EPICmynamesBG/WiFi-USB/firmware/data/power_button_gray_512.png

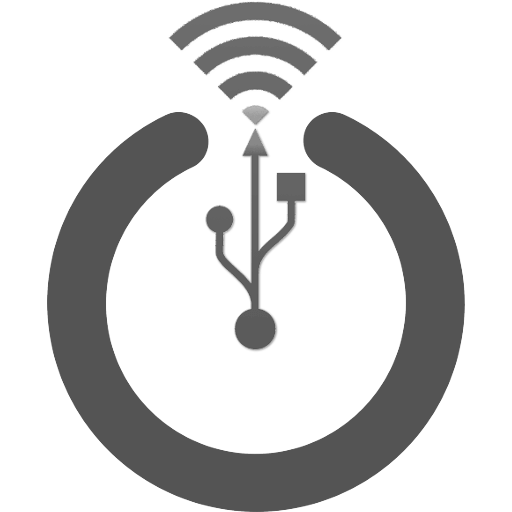
firmware/data/power_button_gray_512.png
