EPICmynamesBG/WiFi-USB/firmware/src/config.h

/**
* WiFi-USB: a wirelessly controllable USB power port
* Author: Brandon Groff
* Version: 1.2
* License: GNU GPLv3 (see LICENSE)
*/
#pragma once

#define SSID "YOUR-WIFI-NAME"

#define SSID_PASSWORD "YOUR-WIFI-PASSWORD"

#define WEBSERVER_DOMAIN "wifiusb" //without the .local ending

#define USB_PIN 2 // the pin that controls USB power

#define AP_SSID "WiFi-USB"

#define AP_PASSWORD "P@$$w0rd"
